unkyulee/esp32-clock/Rev.2/images/003.jpeg

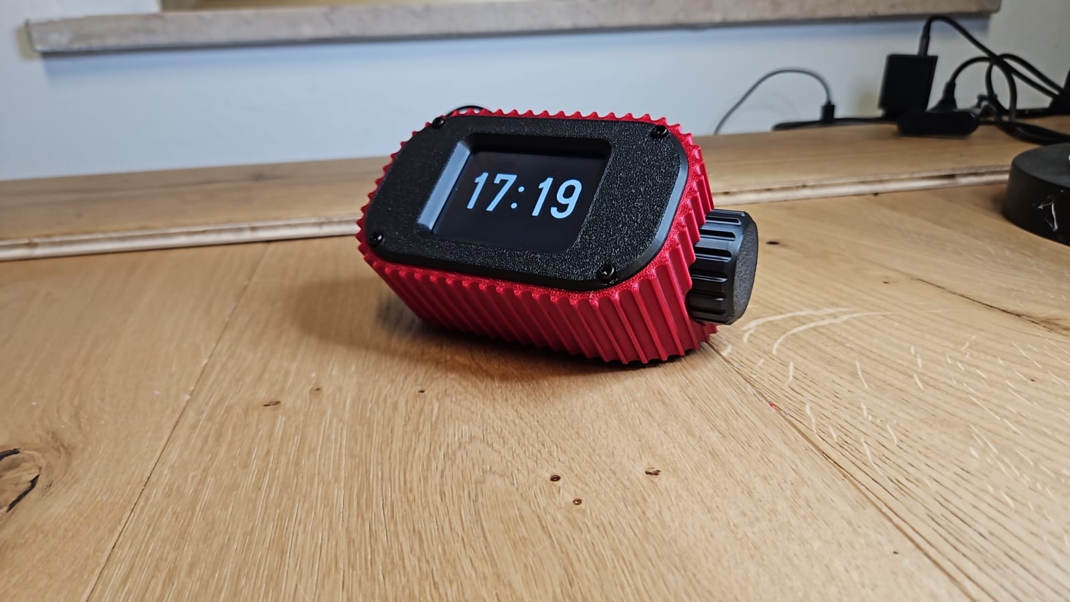
Rev.2/images/003.jpeg
