unkyulee/esp32-clock/Rev.2/images/004.jpeg

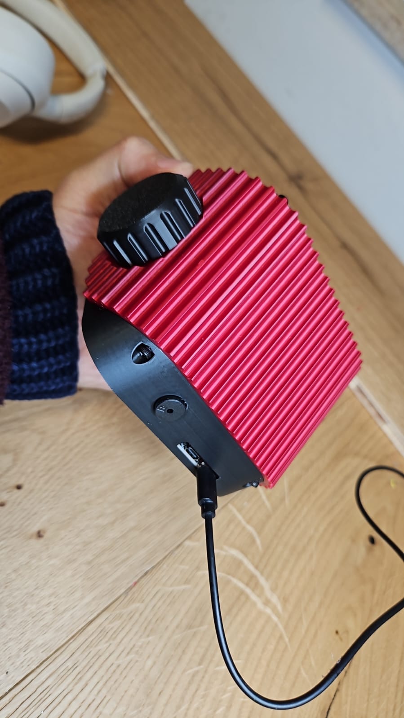
Rev.2/images/004.jpeg
