unkyulee/esp32-clock/Rev.2/platformio/src/service/MassStorage/MassStorage.h

#pragma once

#include <Arduino.h>

#include "USB.h"
#include "USBMSC.h"

#include "esp_partition.h"
#include "wear_levelling.h"

void ms_setup();
void ms_loop();

class FatFSUSBClass
{
public:
    bool setupUSB();
    bool begin();
    void end();
    void unplug();
    bool isConnected();
    bool isHostConnected();
    bool isEjected();

private:
    static void usbEventCallback(
        void *arg,
        esp_event_base_t event_base,
        int32_t event_id,
        void *event_data
    );

    static int32_t readCallback(
        uint32_t lba,
        uint32_t offset,
        void *buffer,
        uint32_t bufsize
    );

    static int32_t writeCallback(
        uint32_t lba,
        uint32_t offset,
        uint8_t *buffer,
        uint32_t bufsize
    );

    static bool startStopCallback(
        uint8_t power_condition,
        bool start,
        bool load_eject
    );

private:
    static USBMSC msc;
    static wl_handle_t wlHandle;
    static uint8_t *sectorBuffer;

    static bool usbStarted;
    static bool usbConfigured;
    static volatile bool hostConnected;
    static bool mediaStarted;
    static bool ejected;

    static uint32_t blockCount;
    static uint16_t blockSize;
    static size_t mediaSize;
};

extern FatFSUSBClass FatFSUSB;
